SSoggy-Group/yamper/hardware/cad/scad/import_wrappers/yamper_v11_3525_speaker_retainer_import.scad

// Quick OpenSCAD wrapper for yamper_v11_3525_speaker_retainer.stl
// Uses the STL from cad/stl. The full mesh source is one folder up.
module yamper_v11_3525_speaker_retainer() {
    import(file = "../../stl/yamper_v11_3525_speaker_retainer.stl", convexity = 10);
}

yamper_v11_3525_speaker_retainer();
