SSoggy-Group/yamper/hardware/cad/scad/import_wrappers/yamper_v11_pisugar_slot_blank_cap_optional_import.scad

// Quick OpenSCAD wrapper for yamper_v11_pisugar_slot_blank_cap_optional.stl
// Uses the STL from cad/stl. The full mesh source is one folder up.
module yamper_v11_pisugar_slot_blank_cap_optional() {
    import(file = "../../stl/yamper_v11_pisugar_slot_blank_cap_optional.stl", convexity = 10);
}

yamper_v11_pisugar_slot_blank_cap_optional();
